sebmorales/ENHP/ENHP_ESP32_code/ExpInHardPef/image.ino

void initImage(){
//  image = "<img src=  \"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">";
  image = "<img src=  \"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">";
}
